kaorii-ako/Poket/blender/ad_40.png

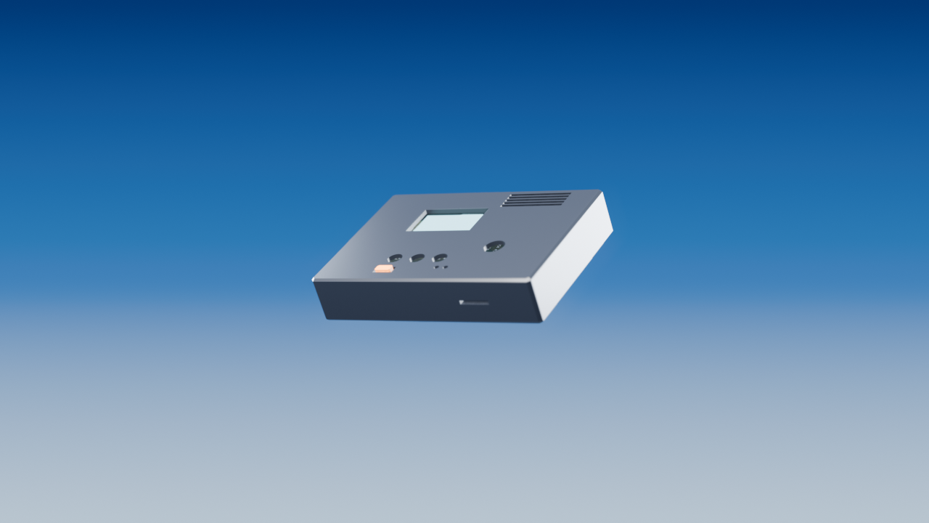
blender/ad_40.png
