kaorii-ako/Poket/blender/ad_170.png

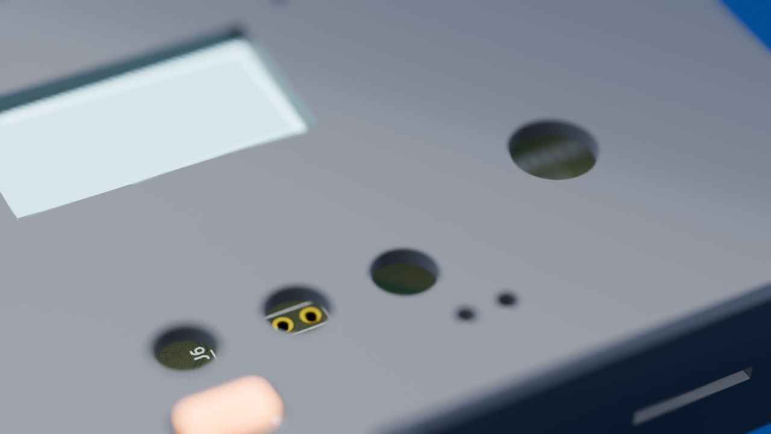
blender/ad_170.png
