kaorii-ako/Poket/blender/ad_290.png

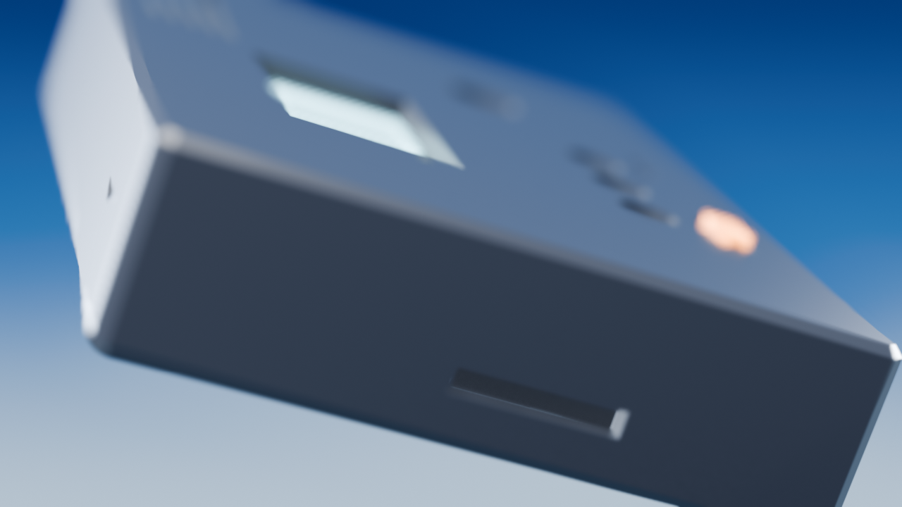
blender/ad_290.png
