kaorii-ako/Poket/blender/ad_400.png

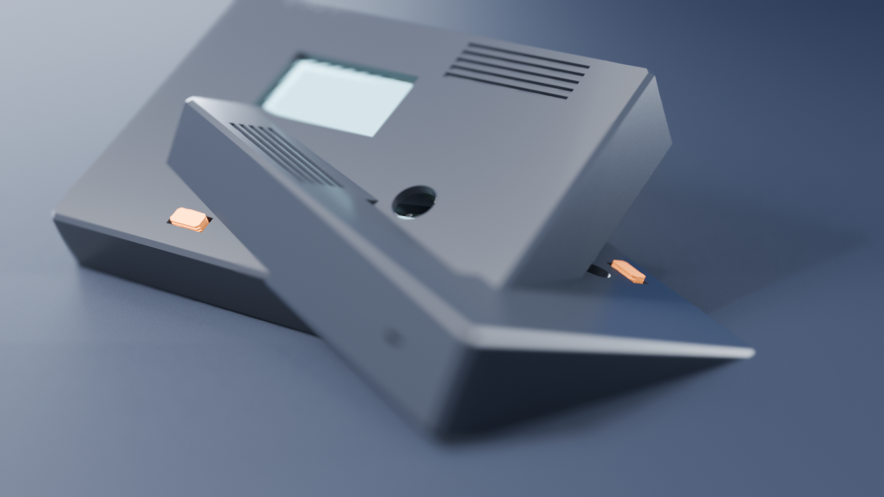
blender/ad_400.png
