kaorii-ako/Poket/blender/ad_510.png

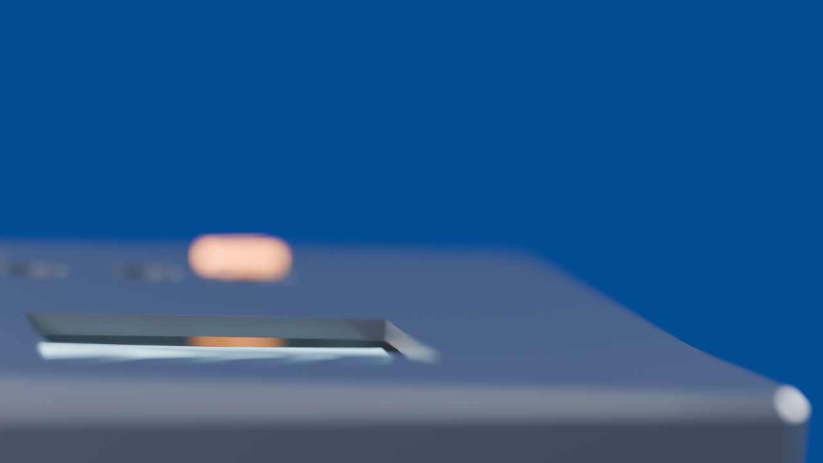
blender/ad_510.png
