kaorii-ako/Poket/blender/ad_660.png

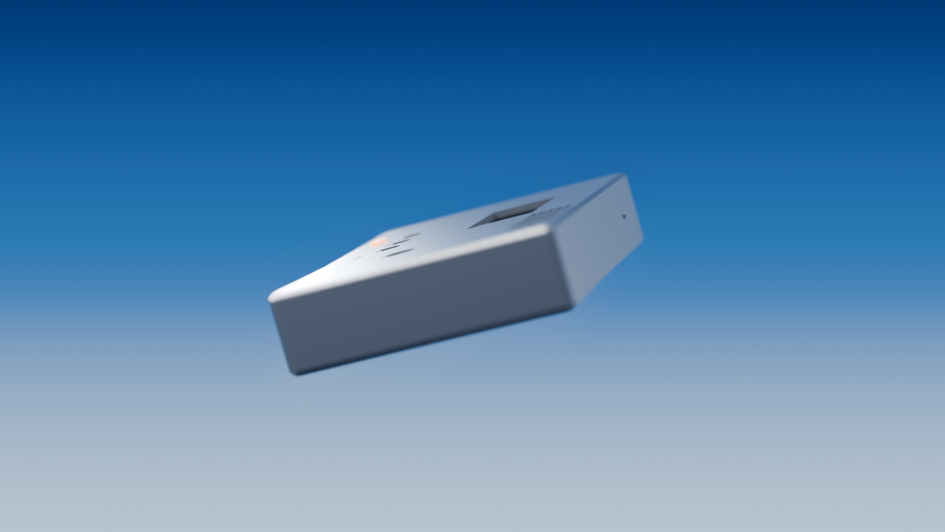
blender/ad_660.png
