kaorii-ako/Poket/blender/shot_40.png

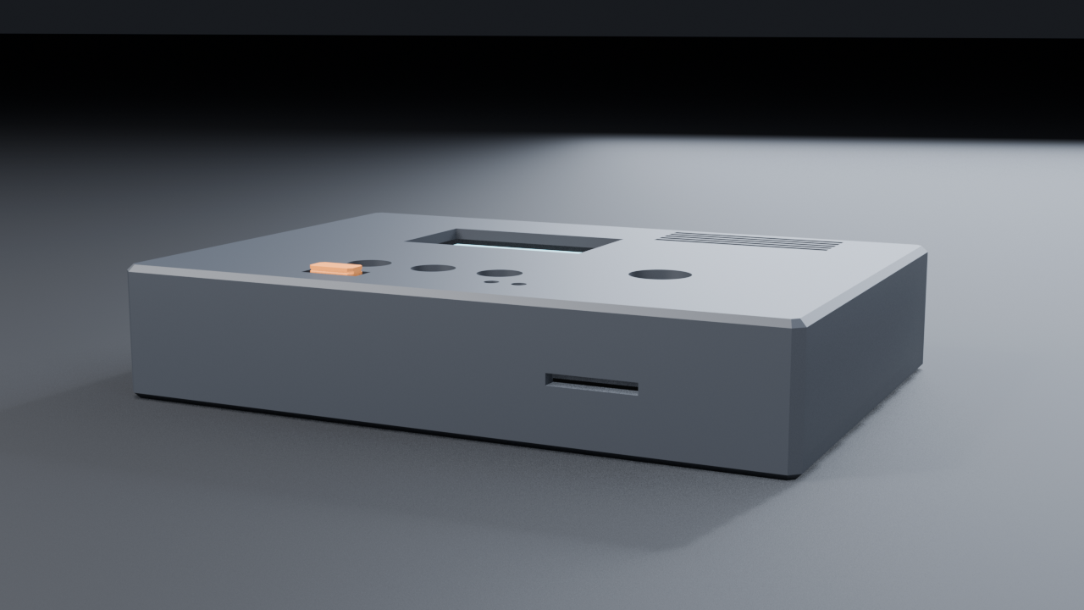
blender/shot_40.png
