kaorii-ako/Poket/blender/shot_150.png

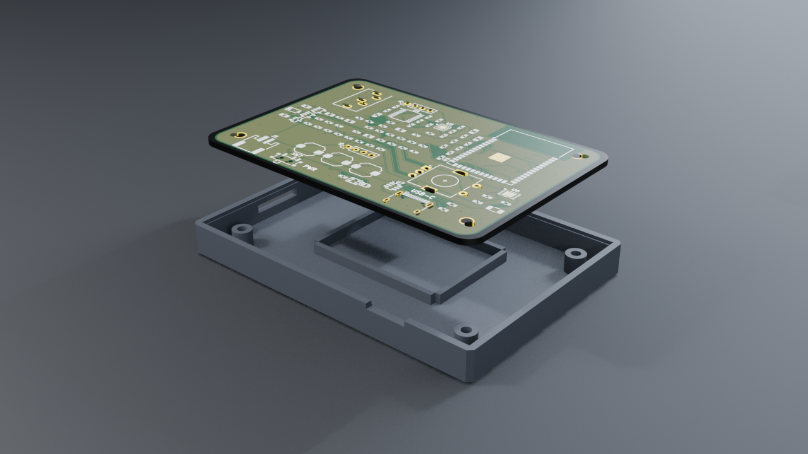
blender/shot_150.png
