kaorii-ako/Poket/blender/shot_230.png

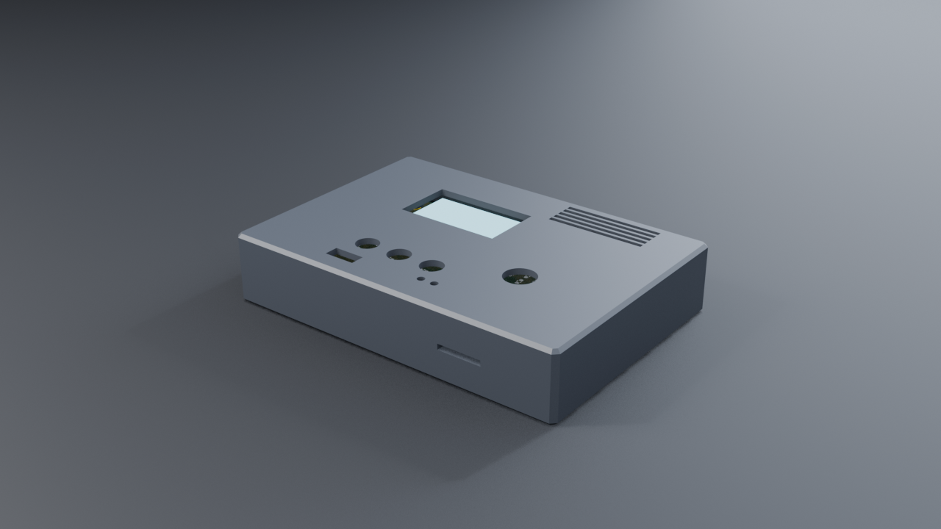
blender/shot_230.png
