kaorii-ako/Poket/blender/shot_320.png

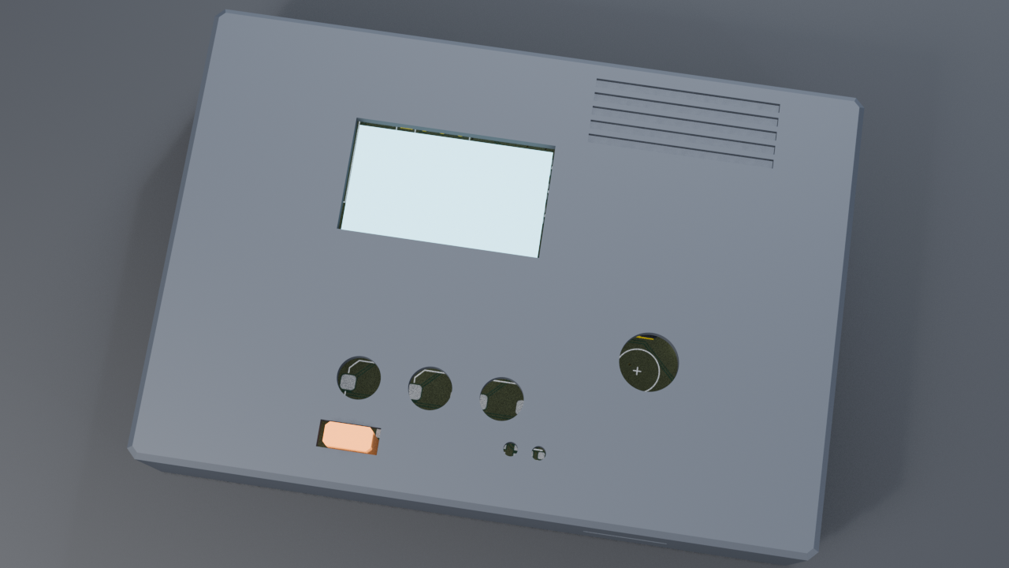
blender/shot_320.png
