kaorii-ako/Poket/blender/shot_440.png

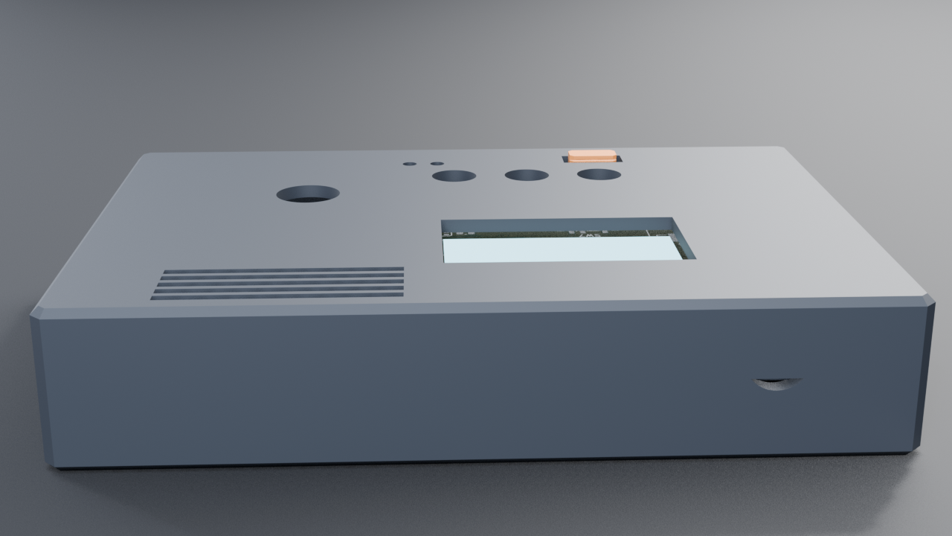
blender/shot_440.png
