kaorii-ako/Poket/blender/shot_580.png

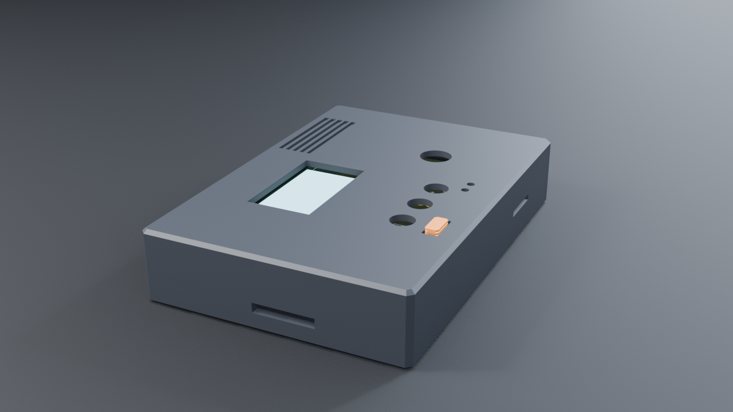
blender/shot_580.png
