kaorii-ako/Poket/blender/tex/pcb-bottom.png

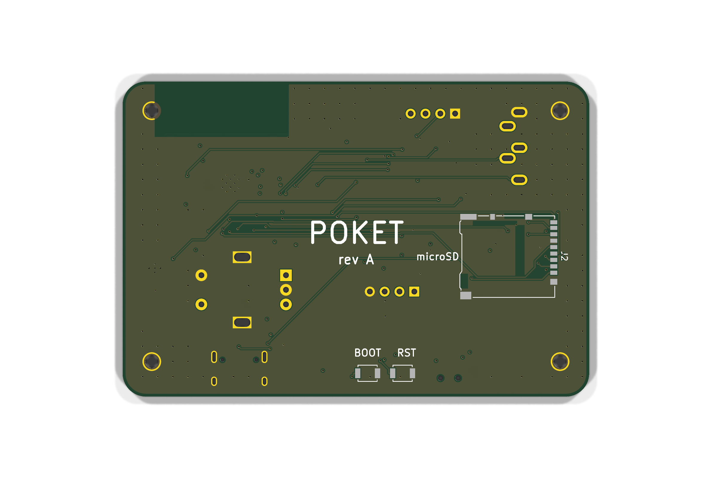
blender/tex/pcb-bottom.png
