kaorii-ako/Poket/blender/tex/pcb-top.png

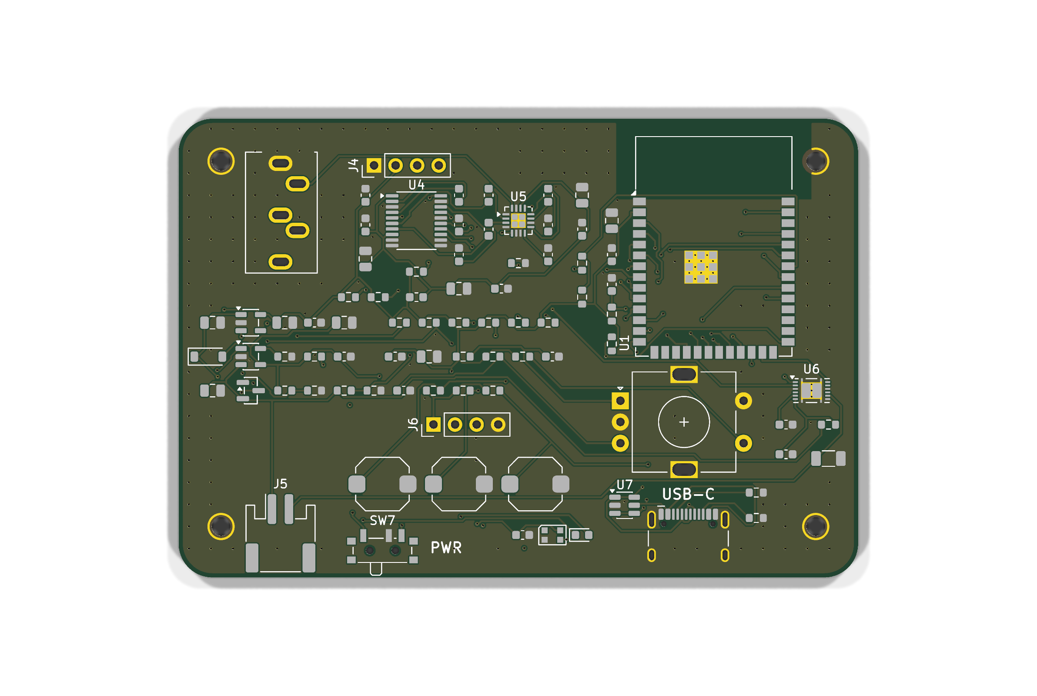
blender/tex/pcb-top.png
