kaorii-ako/Poket/images/case-back-iso.png

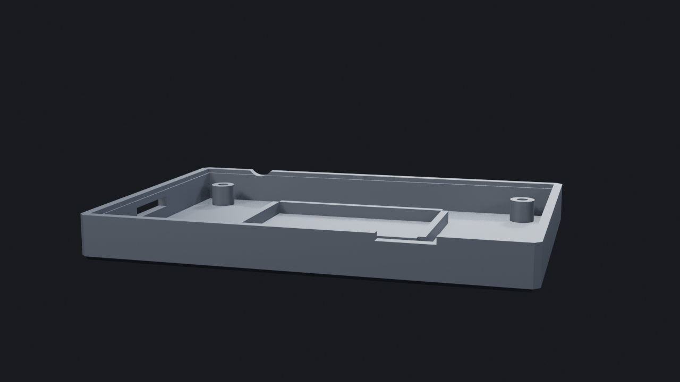
images/case-back-iso.png
