kaorii-ako/Poket/firmware/main/drivers/i2c_bus.c

#include "drivers/i2c_bus.h"
#include "board.h"
#include "esp_log.h"

static i2c_master_bus_handle_t s_bus;

esp_err_t i2c_bus_init(void) {
    if (s_bus) return ESP_OK;
    i2c_master_bus_config_t cfg = {
        .i2c_port = I2C_NUM_0,
        .sda_io_num = PIN_I2C_SDA,
        .scl_io_num = PIN_I2C_SCL,
        .clk_source = I2C_CLK_SRC_DEFAULT,
        .glitch_ignore_cnt = 7,
        .flags.enable_internal_pullup = false,   // 4.7k externals are fitted
    };
    return i2c_new_master_bus(&cfg, &s_bus);
}

esp_err_t i2c_dev_add(uint8_t addr, uint32_t hz, i2c_master_dev_handle_t *out) {
    i2c_device_config_t d = {
        .dev_addr_length = I2C_ADDR_BIT_LEN_7,
        .device_address = addr,
        .scl_speed_hz = hz,
    };
    return i2c_master_bus_add_device(s_bus, &d, out);
}
